davidpty/benchpilot/src/wifi_config.example.h

// WiFi Configuration — copy this file to wifi_config.h and set your credentials
#ifndef WIFI_CONFIG_H
#define WIFI_CONFIG_H

#define WIFI_SSID      "your_wifi_name"
#define WIFI_PASSWORD  "your_wifi_password"

#endif
